jonolt/dmx-colormatch/firmware2/src/fsmmain.h

#ifndef FSMMAIN_H
#define FSMMAIN_H

#include <Automaton.h>


class FsmMain: public Machine
{
    public:
        FsmMain( void ) : Machine() {};

        enum { PAGE_1, PAGE_2, PAGE_3, PAGE_4, PAGE_5 }; // STATES
        enum { SW1, SW2, SW3, SW4, SW5, SW6, SW7, SW8, ELSE }; // EVENTS
        enum { ENT_1, LOOP_1, EXIT_1, ENT_2, LOOP_2, EXIT_2, ENT_3, LOOP_3, EXIT_3, ENT_4, LOOP_4, EXIT_4,}; // ACTIONS

        FsmMain & begin();
        FsmMain & trace( Stream & stream );
        int event( int id );
        void action( int id );

    protected:

    private:
};

#endif // FSMMAIN_H
