jonolt/dmx-colormatch/firmware2/src/parandvals.cpp

#include "parandvals.h"

ParAndVals::ParAndVals()
{
    colorChanels = EEPROM.read(ADD_COLOR_CHANELS);
    startAddress = EEPROM.read(ADD_START_ADDRESS);
    activeRegister = EEPROM.read(ADD_REF_REGISTER);
    waitForSerialFlag = (bool) EEPROM.read(ADD_WAIT_FOR_SERIAL);
}
