jonolt/dmx-colormatch/firmware2/src/Atm_button_IO.h

//based on Atm_button from Automaton by tinkerspy

#pragma once

#include <Arduino.h>
#include "Automaton.h"


class Atm_button_custom : public Machine
{
public:
    enum { IDLE, WAIT, PRESSED, REPEAT, RELEASE, LIDLE, LWAIT, LPRESSED, LRELEASE, WRELEASE, AUTO_ST };
    enum { EVT_LMODE, EVT_TIMER, EVT_DELAY, EVT_REPEAT, EVT_PRESS, EVT_RELEASE, EVT_COUNTER, EVT_AUTO, ELSE };
    enum { BTN_PASS4 = -4, BTN_PASS3 = -3, BTN_PASS2 = -2, BTN_PASS1 = -1, BTN_RELEASE = 0, BTN_PRESS1 = 1, BTN_PRESS2 = 2, BTN_PRESS3 = 3, BTN_PRESS4 = 4 };

    Atm_button_custom( void ) : Machine() {};
    Atm_button_custom& begin( int attached_pin );
    Atm_button_custom& trace( Stream& stream );
    Atm_button_custom& onPress( atm_cb_push_t callback, int idx = 0 );
    Atm_button_custom& onPress( Machine& machine, int event = 0 );
    Atm_button_custom& onPress( int id, atm_cb_push_t callback, int idx = 0 );
    Atm_button_custom& onPress( int id, Machine& machine, int event = 0 );
    Atm_button_custom& onRelease( atm_cb_push_t callback, int idx = 0 );
    Atm_button_custom& onRelease( Machine& machine, int event = 0 );
    Atm_button_custom& debounce( int delay );
    Atm_button_custom& longPress( int max, int delay );
    Atm_button_custom& repeat( int delay = 500, int speed = 50 );
    Atm_button_custom& autoPress( int delay, int press = 1 );

    void pinModeCustom(uint8_t pin, PinMode mode);
    PinStatus digitalReadCustom(uint8_t pin);

protected:
    enum { ENT_PRESS, ENT_RELEASE, ENT_LSTART, ENT_LCOUNT, ENT_LRELEASE, EXT_WRELEASE, ENT_AUTO };
    static const int DEBOUNCE = 5;
    atm_connector onpress, onrelease;
    atm_connector longpress[2];
    short pin;

    atm_timer_millis timer_debounce, timer_delay, timer_repeat, timer_auto;
    atm_counter counter_longpress;
    int longpress_max;
    int auto_press = 1;

    int event( int id );
    void action( int id );
};
